ApexHAB/apex-alpha/launches/launch-1/maps+graphs/graph-altitude.jpg

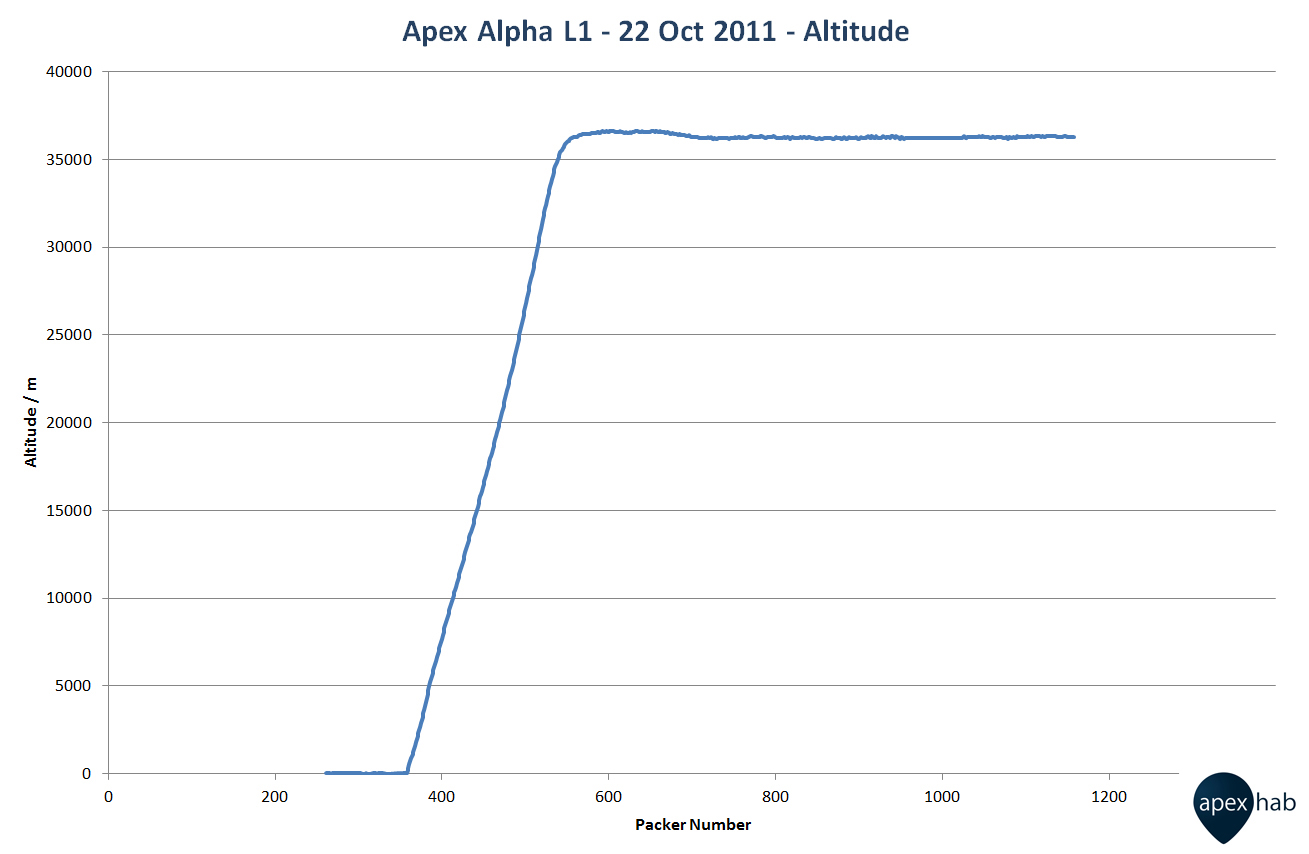
launches/launch-1/maps+graphs/graph-altitude.jpg
