ApexHAB/apex-alpha/launches/launch-1/maps+graphs/graph-battery-voltage.jpg

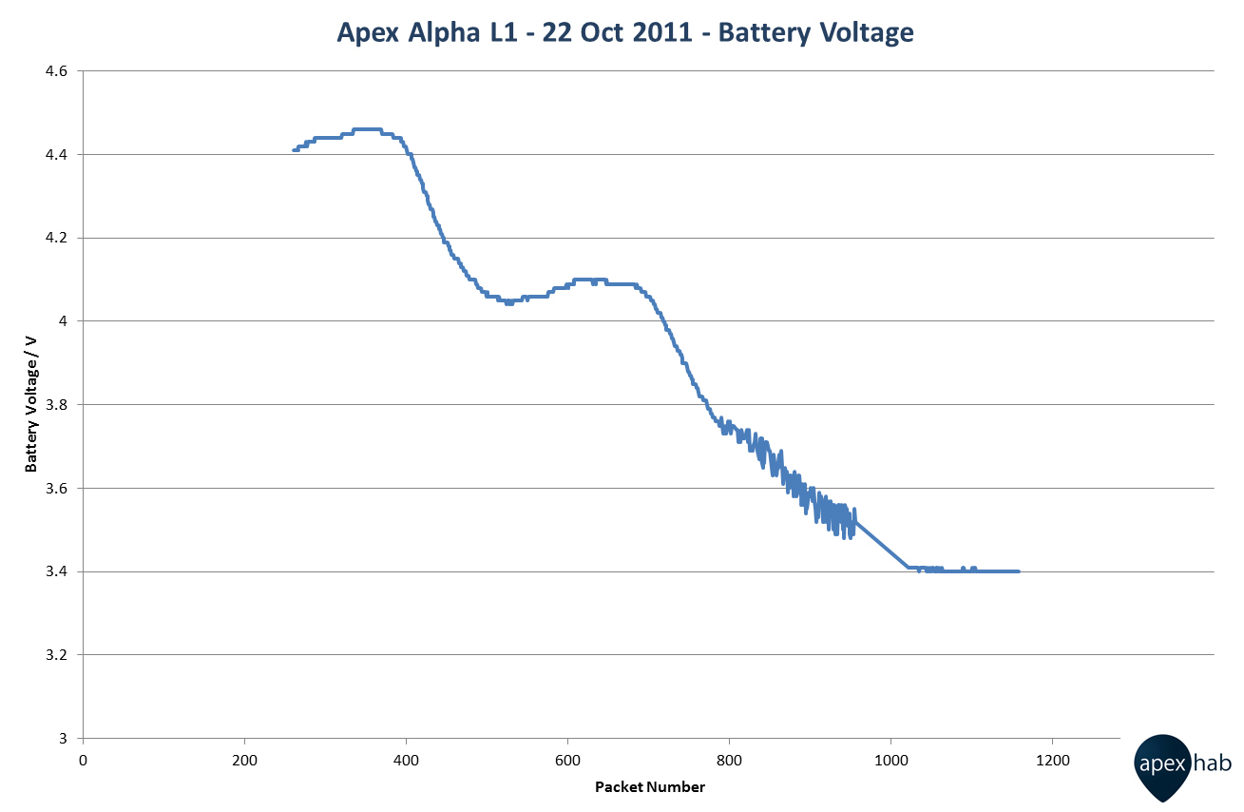
launches/launch-1/maps+graphs/graph-battery-voltage.jpg
