ApexHAB/apex-alpha/launches/launch-1/maps+graphs/graph-satellites.jpg

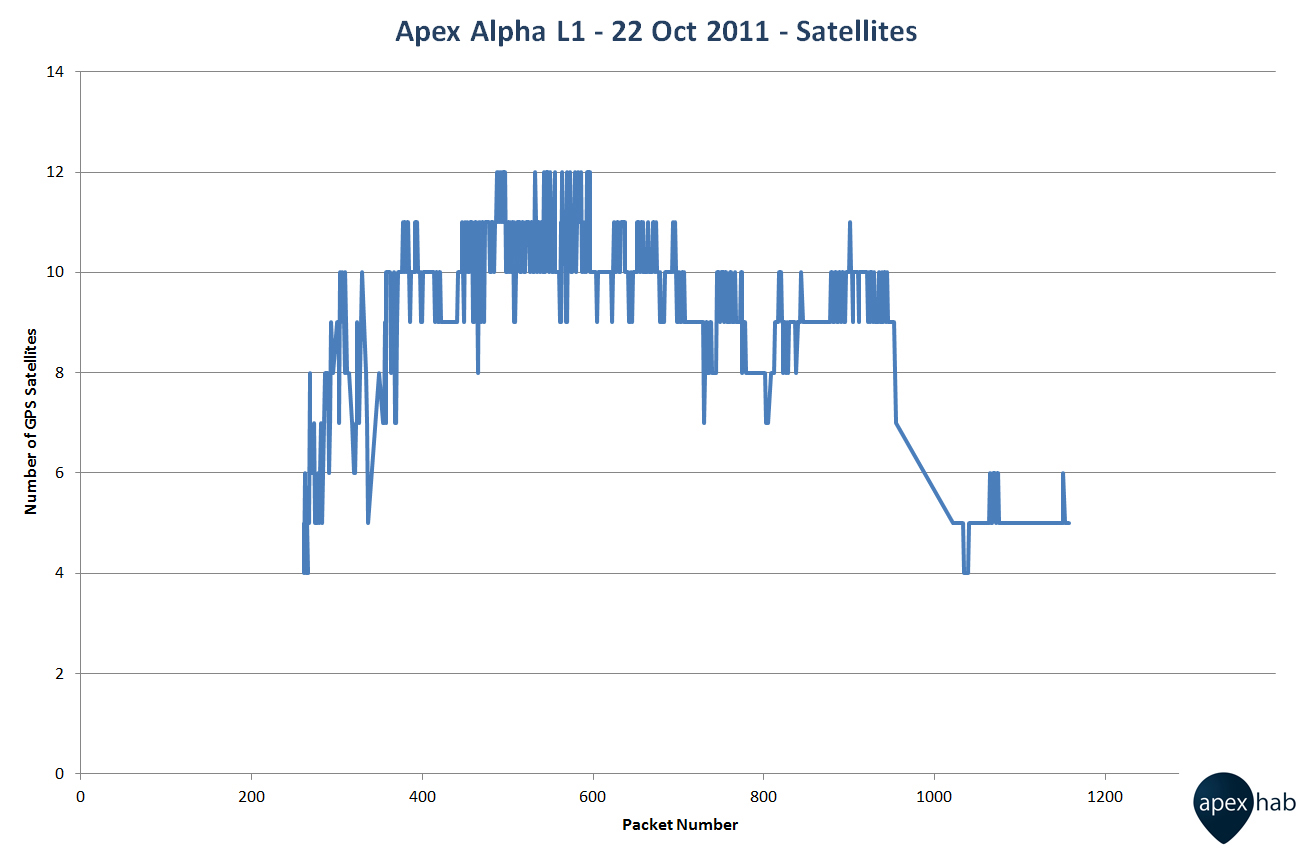
launches/launch-1/maps+graphs/graph-satellites.jpg
