ApexHAB/apex-alpha/launches/launch-1/maps+graphs/map-1.jpg

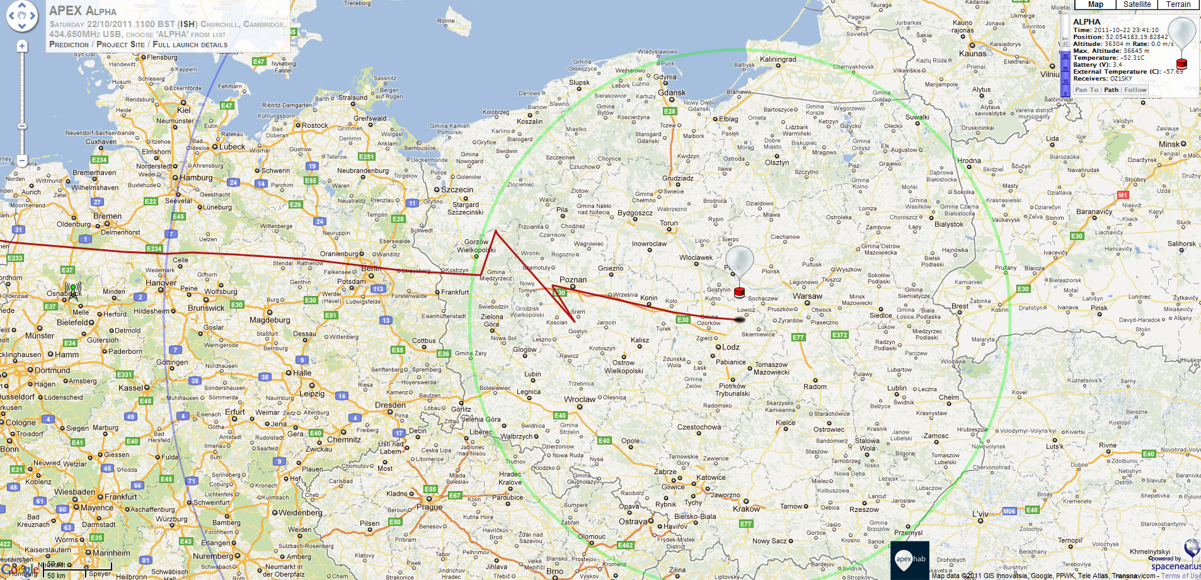
launches/launch-1/maps+graphs/map-1.jpg
