ApexHAB/apex-alpha/launches/launch-1/maps+graphs/map-3.jpg

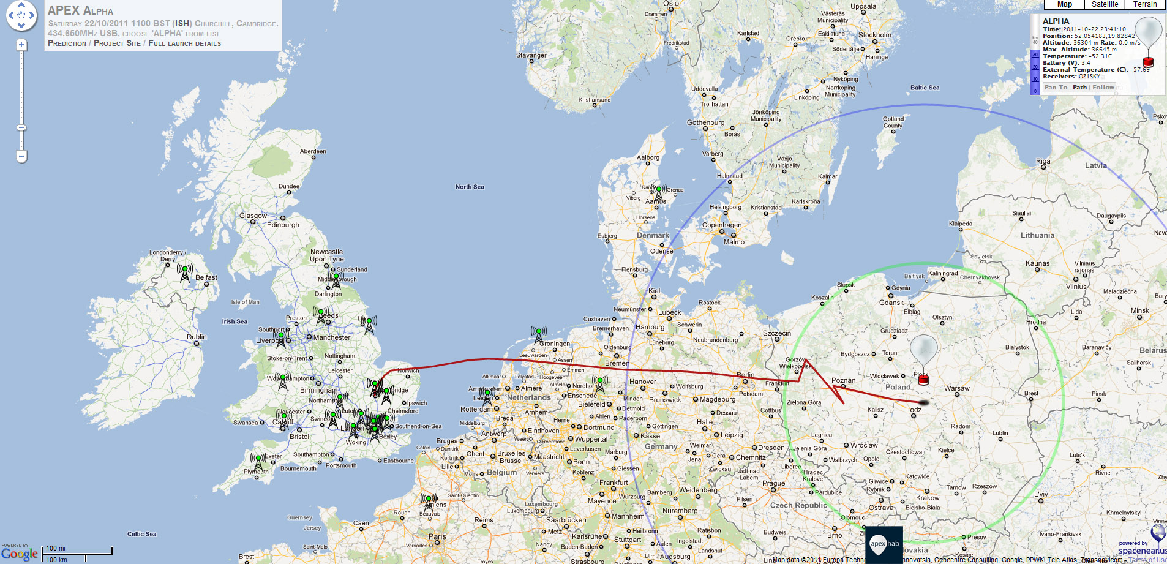
launches/launch-1/maps+graphs/map-3.jpg
