ApexHAB/apex-alpha/launches/launch-1/maps+graphs/map-4.jpg

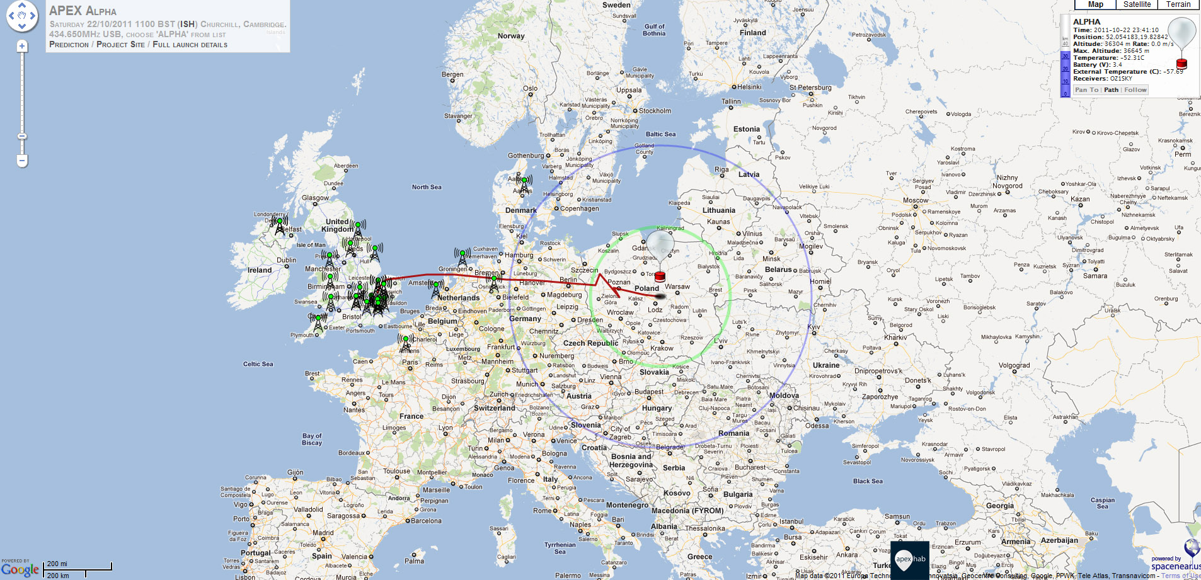
launches/launch-1/maps+graphs/map-4.jpg
