ApexHAB/apex-alpha/launches/launch-1/maps+graphs/track-1.jpg

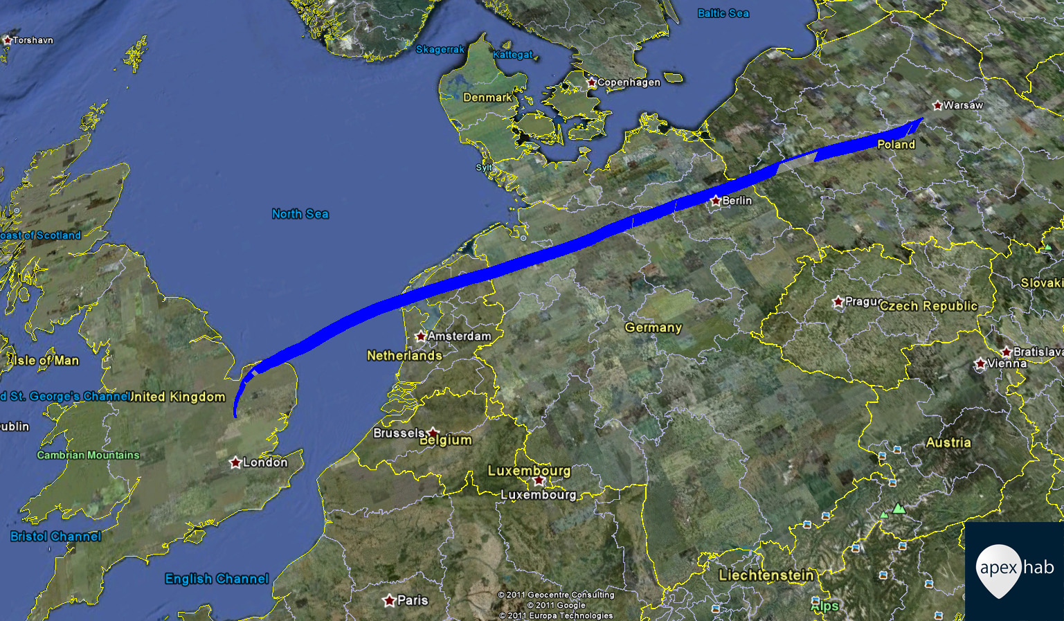
launches/launch-1/maps+graphs/track-1.jpg
