ApexHAB/apex-alpha/launches/launch-1/maps+graphs/track-2.jpg

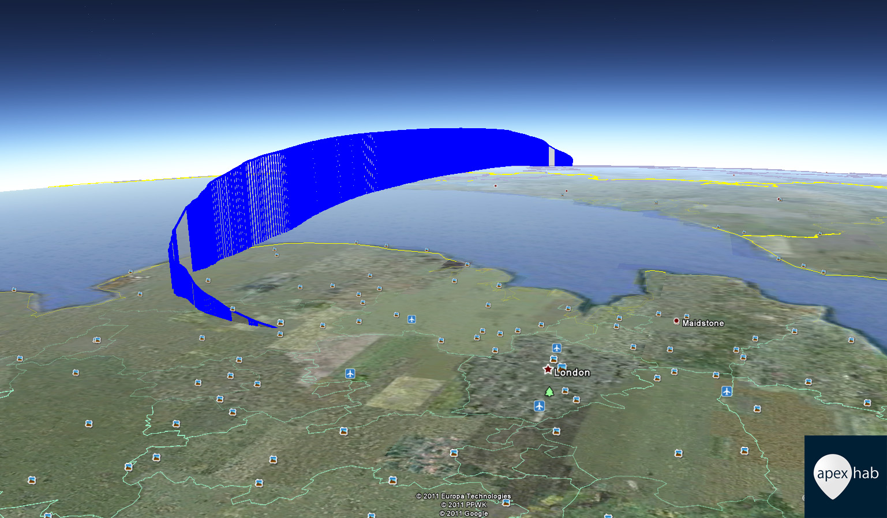
launches/launch-1/maps+graphs/track-2.jpg
