ApexHAB/apex-alpha/pcb/rev1.0/pcb.png

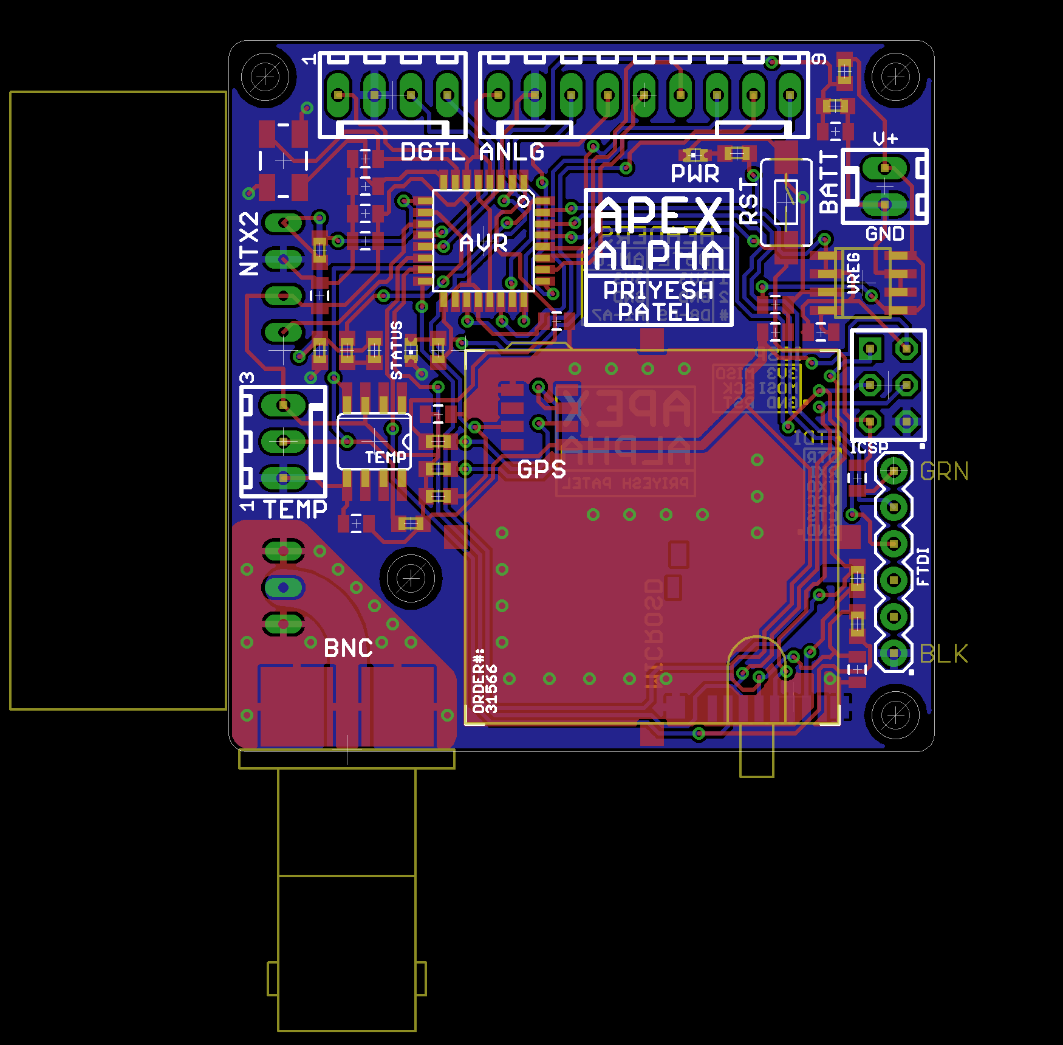
pcb/rev1.0/pcb.png
