ApexHAB/apex-alpha/guide/alpha-diagram.jpg

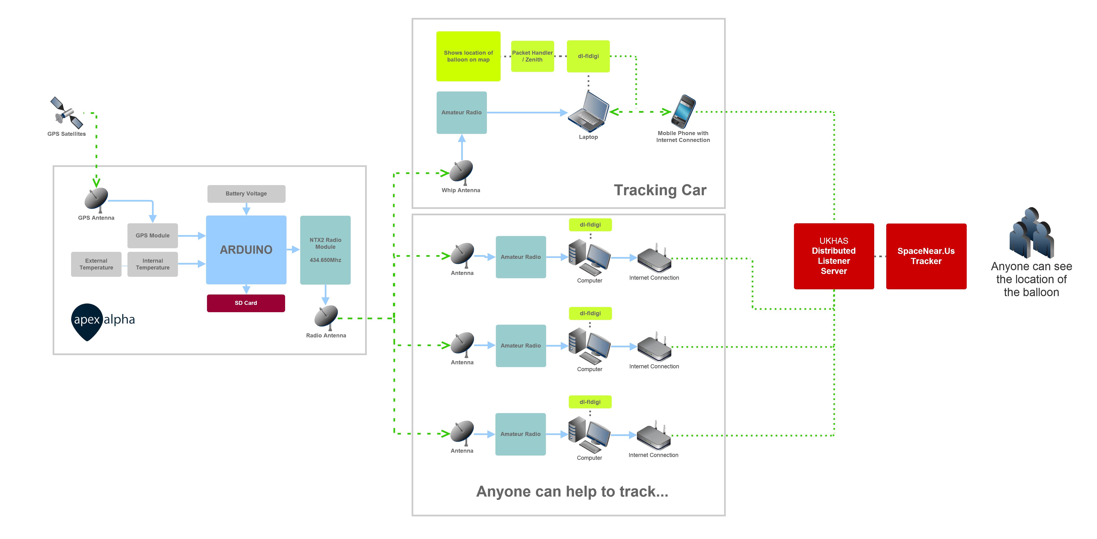
guide/alpha-diagram.jpg
