ApexHAB/apex-alpha/firmware/alpha/battery.h

/**
 * battery.h
 *
 * Part of the Apex Alpha project
 * http://www.apexhab.org/alpha/
 *
 * Priyesh Patel
 *
 * (c) Copyright ApexHAB 2011
 * team@apexhab.org
 */

#ifndef BATTERY_H
#define BATTERY_H

#include "WProgram.h"

#define BATTERY_PIN 0
/*
 * R1 = 33K
 * R2 = 22K
 *
 * Ratio = R2 / (R1 + R2)
 */
#define BATTERY_RESISTOR_RATIO 0.4
#define BATTERY_REFERENCE_VOLTS 3.3

float battery_get_voltage();

#endif
