ApexHAB/apex-alpha/firmware/alpha/counter.cpp

/**
 * counter.cpp
 *
 * Part of the Apex Alpha project
 * http://www.apexhab.org/alpha/
 *
 * Priyesh Patel
 *
 * (c) Copyright ApexHAB 2011
 * team@apexhab.org
 */

#include "counter.h"

uint16_t counter_get()
{
    byte lowByte = EEPROM.read(EEPROM_LOW_BYTE);
    byte highByte = EEPROM.read(EEPROM_HIGH_BYTE);
    return ((highByte << 8) | lowByte);
}

void counter_set(uint16_t new_counter)
{
    EEPROM.write(EEPROM_LOW_BYTE, (byte) (0xFF & new_counter));
    EEPROM.write(EEPROM_HIGH_BYTE, (byte) (new_counter >> 8));
}

void counter_inc()
{
    counter_set(counter_get() + 1);
}

void counter_reset()
{
    counter_set(0);
}
