ApexHAB/apex-alpha/firmware/alpha/Temp.h

/**
 * Temp.h
 *
 * Part of the Apex Alpha project
 * http://www.apexhab.org/alpha/
 *
 * Priyesh Patel
 *
 * (c) Copyright ApexHAB 2011
 * team@apexhab.org
 */

#ifndef TEMP_H
#define TEMP_H

#include "WProgram.h"
#include "OneWire.h"

class Temp
{
    public:
        Temp();
        void init(int pin);
        float get(uint8_t* addr);
    private:
        int _pin;
};

#endif
